doneill890/slide-whistle/docs/assets/img/fan_piece1.jpg

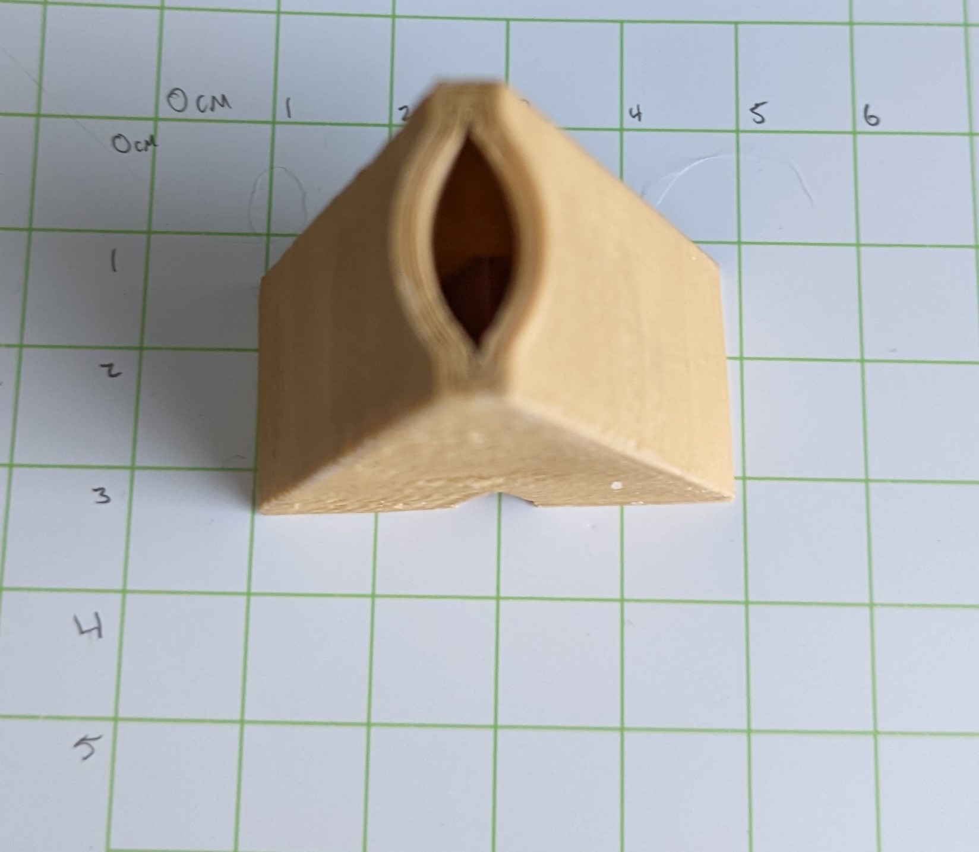
docs/assets/img/fan_piece1.jpg
