doneill890/slide-whistle/docs/assets/img/fan_piece2.jpg

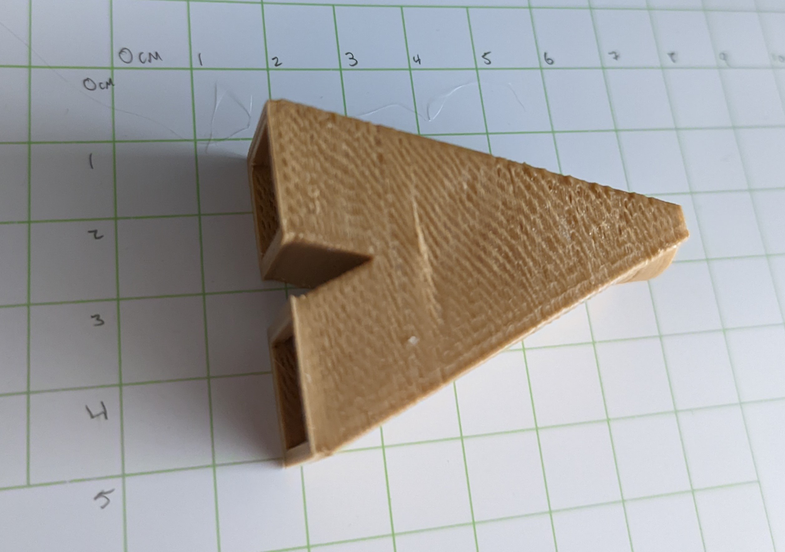
docs/assets/img/fan_piece2.jpg
