doneill890/slide-whistle/docs/assets/img/PXL_20221207_054933590.jpg

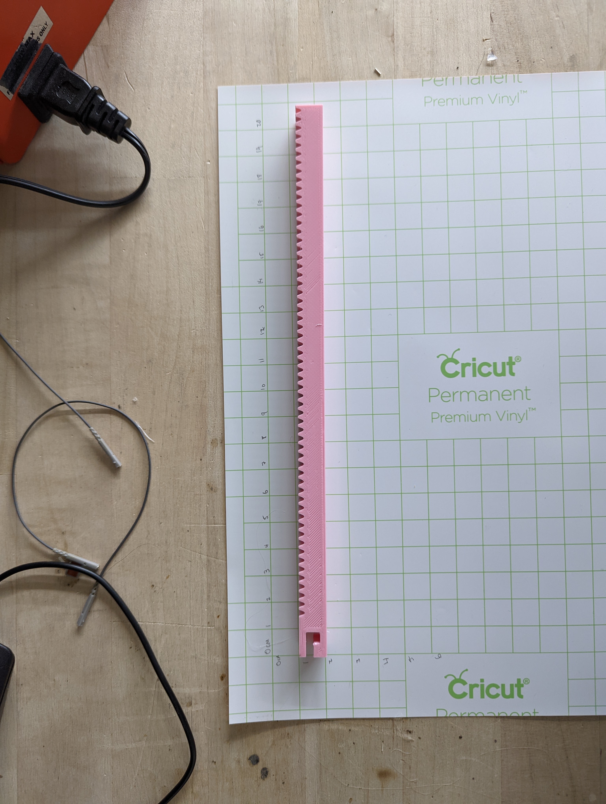
docs/assets/img/PXL_20221207_054933590.jpg
